NeuroTinker/NeuroBytes_Motor_Neuron/HARDWARE/copper.png

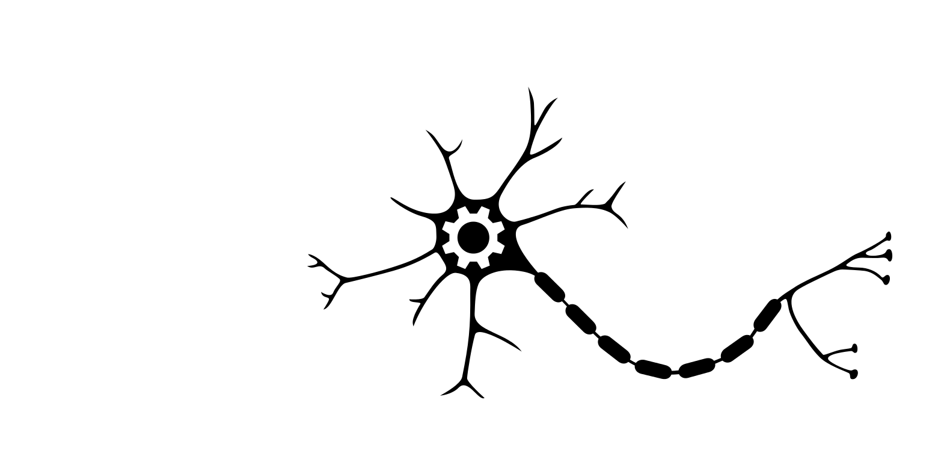
HARDWARE/copper.png
